mohamedboubaker/GPS-Tracker/PCB/JLCPCB Support/Produce_DanZhi.SMT_Snapshot.Top.2993670A_Y4.SMT02212041048436.png

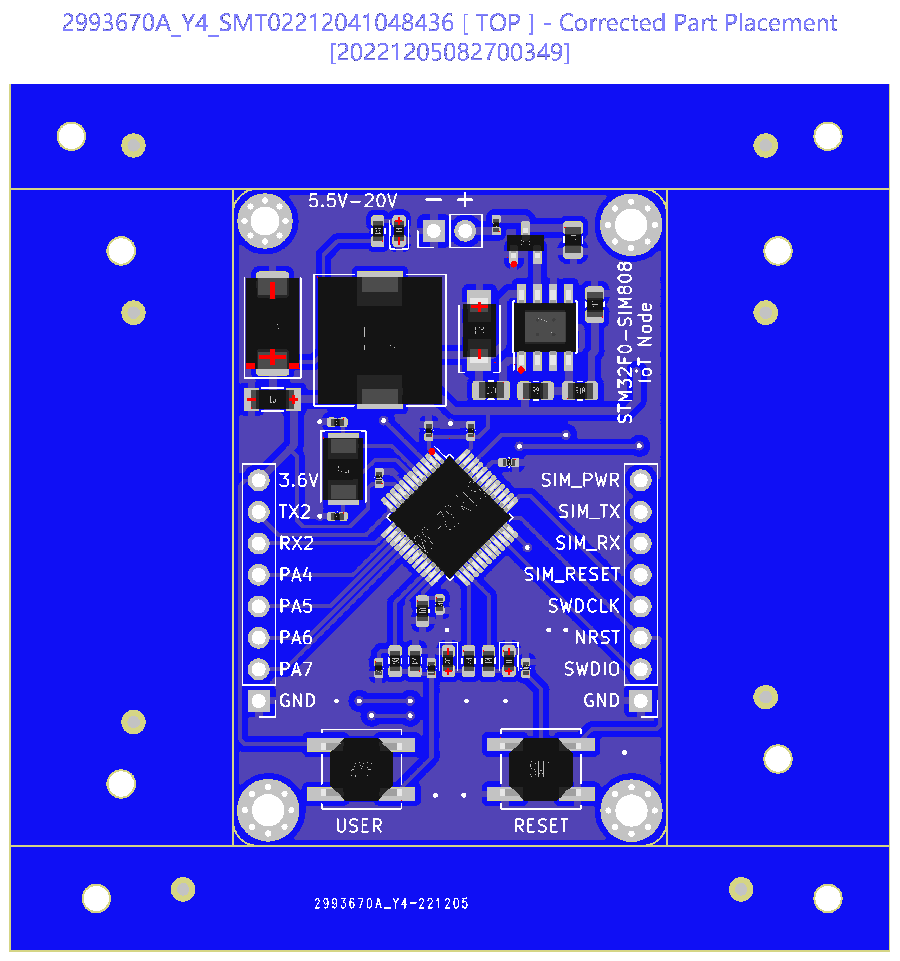
PCB/JLCPCB Support/Produce_DanZhi.SMT_Snapshot.Top.2993670A_Y4.SMT02212041048436.png
