mohamedboubaker/GPS-Tracker/PCB/layout.png

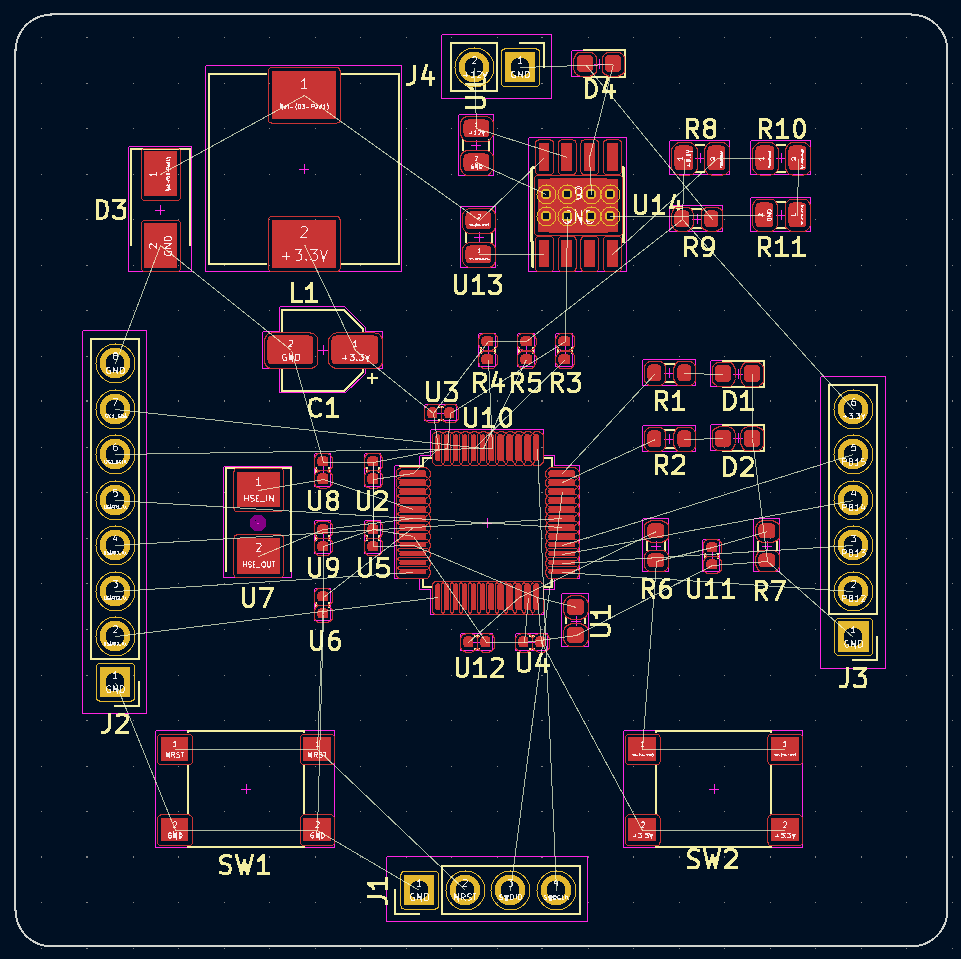
PCB/layout.png
