mohamedboubaker/GPS-Tracker/Pictures/3D_backside.png

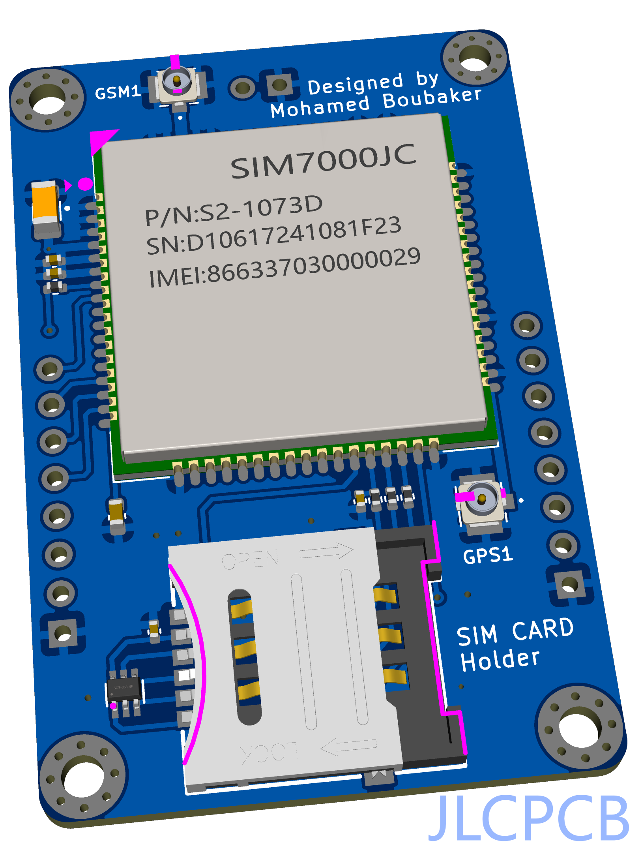
Pictures/3D_backside.png
