mohamedboubaker/GPS-Tracker/Pictures/Layout_FrontAndBack.png

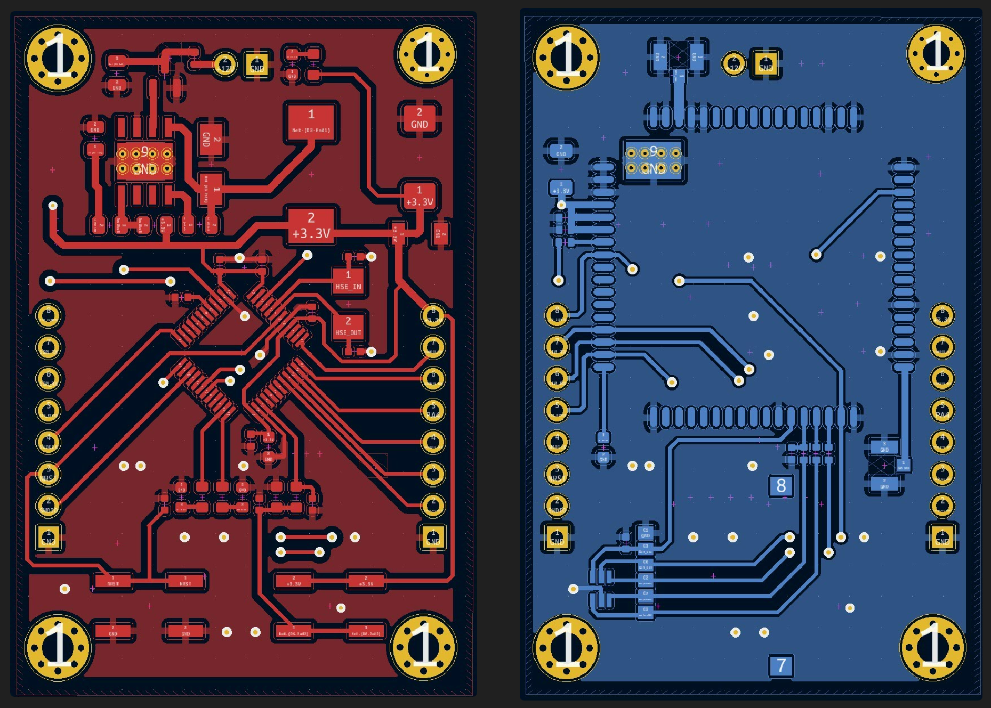
Pictures/Layout_FrontAndBack.png
