mohamedboubaker/GPS-Tracker/Pictures/layout_frontside.png

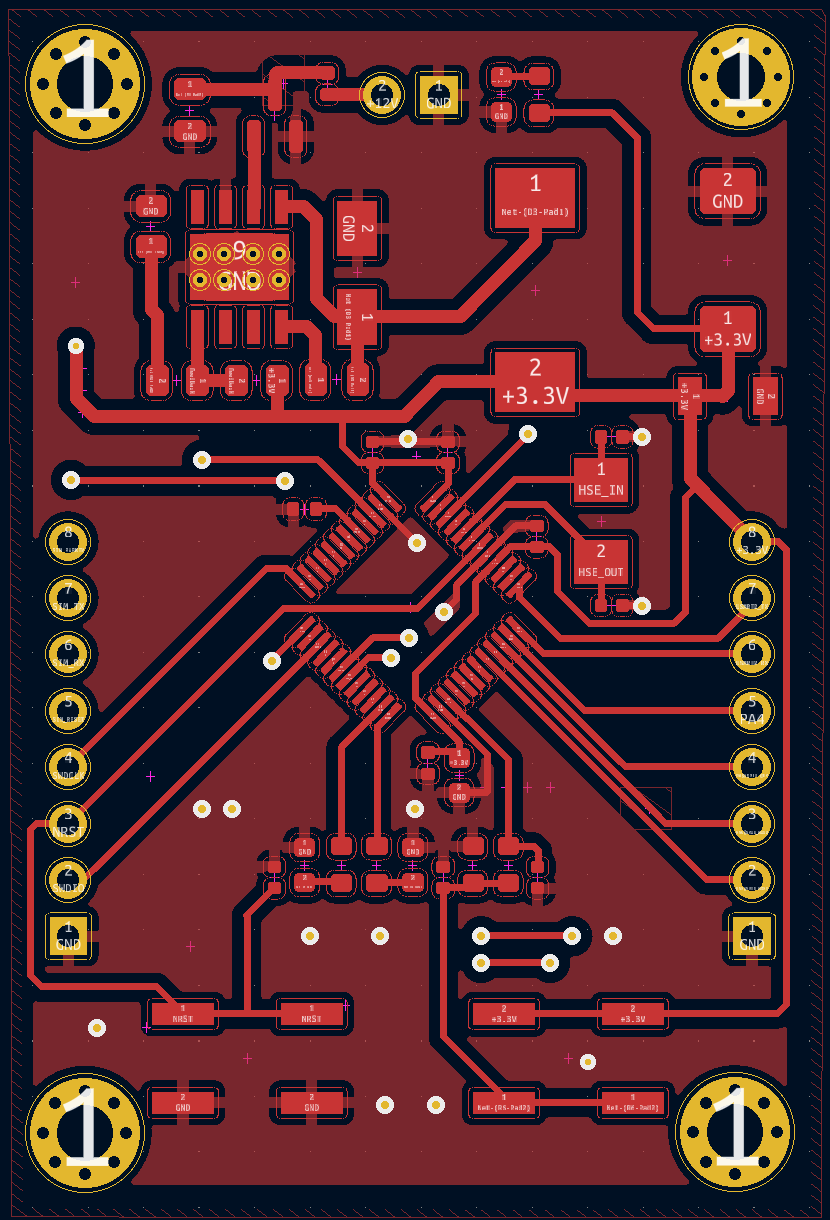
Pictures/layout_frontside.png
