mohamedboubaker/GPS-Tracker/Pictures/test_drive_1.jpeg

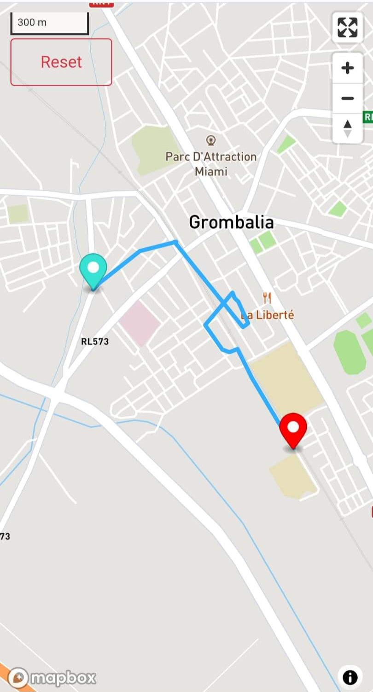
Pictures/test_drive_1.jpeg
