mohamedboubaker/GPS-Tracker/Pictures/test_drive_nuremberg.png

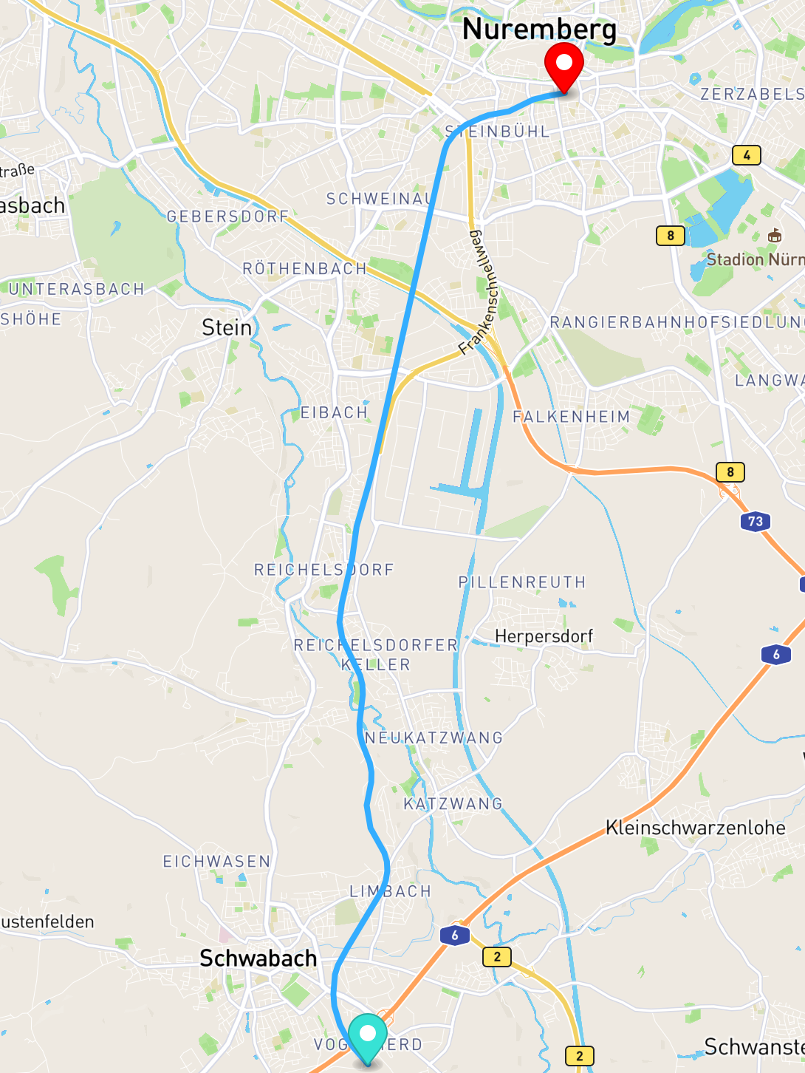
Pictures/test_drive_nuremberg.png
