mohamedboubaker/GPS-Tracker/Pictures/test_drive_nuremberg_munich.png

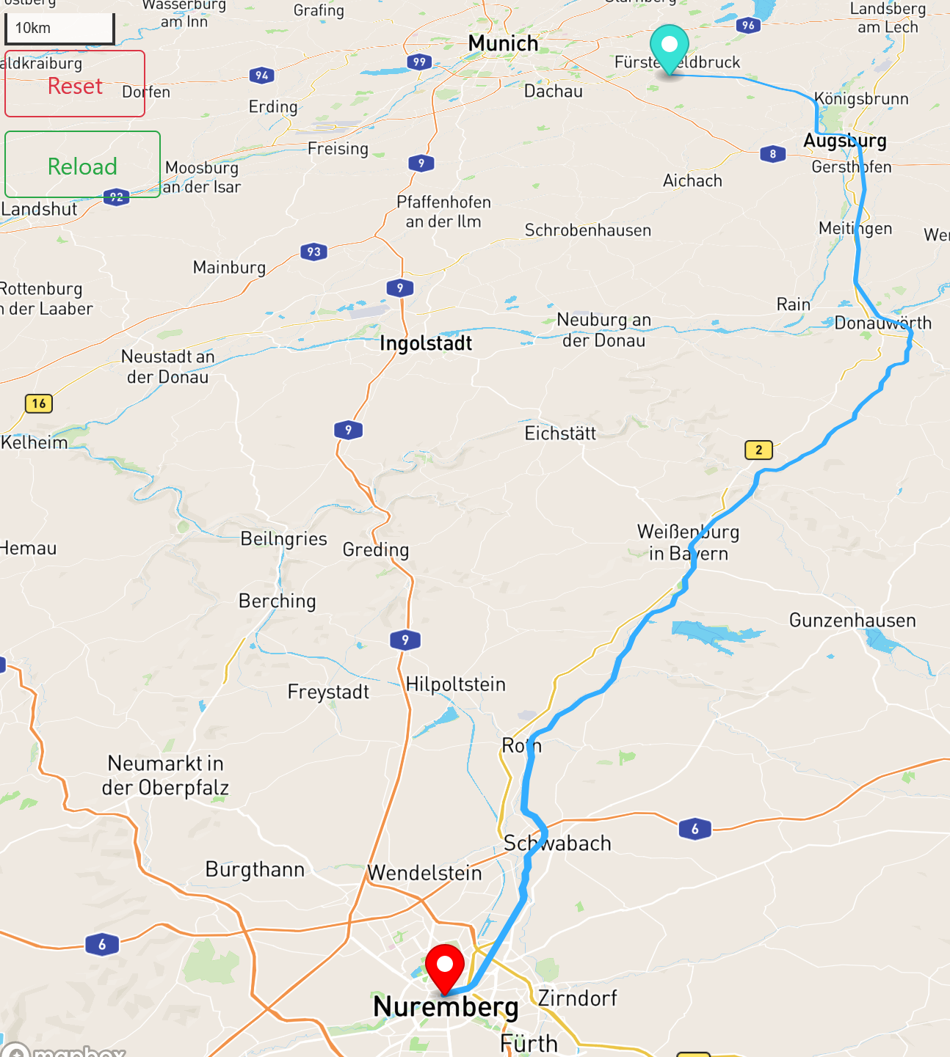
Pictures/test_drive_nuremberg_munich.png
